kanflo/esparducam/arducam/ov2640_regs.h

#ifndef OV2640_REGS_H
#define OV2640_REGS_H
#include "arducam.h"

const struct sensor_reg OV2640_QVGA[] PROGMEM =
{
	{0xff, 0x0}, 
	{0x2c, 0xff}, 
	{0x2e, 0xdf}, 
	{0xff, 0x1}, 
	{0x3c, 0x32}, 
	{0x11, 0x0}, 
	{0x9, 0x2}, 
	{0x4, 0xa8}, 
	{0x13, 0xe5}, 
	{0x14, 0x48}, 
	{0x2c, 0xc}, 
	{0x33, 0x78}, 
	{0x3a, 0x33}, 
	{0x3b, 0xfb}, 
	{0x3e, 0x0}, 
	{0x43, 0x11}, 
	{0x16, 0x10}, 
	{0x39, 0x2}, 
	{0x35, 0x88}, 

	{0x22, 0xa}, 
	{0x37, 0x40}, 
	{0x23, 0x0}, 
	{0x34, 0xa0}, 
	{0x6, 0x2}, 
	{0x6, 0x88}, 
	{0x7, 0xc0}, 
	{0xd, 0xb7}, 
	{0xe, 0x1}, 
	{0x4c, 0x0}, 
	{0x4a, 0x81}, 
	{0x21, 0x99}, 
	{0x24, 0x40}, 
	{0x25, 0x38}, 
	{0x26, 0x82}, 
	{0x5c, 0x0}, 
	{0x63, 0x0}, 
	{0x46, 0x22}, 
	{0xc, 0x3a}, 
	{0x5d, 0x55}, 
	{0x5e, 0x7d}, 
	{0x5f, 0x7d}, 
	{0x60, 0x55}, 
	{0x61, 0x70}, 
	{0x62, 0x80}, 
	{0x7c, 0x5}, 
	{0x20, 0x80}, 
	{0x28, 0x30}, 
	{0x6c, 0x0}, 
	{0x6d, 0x80}, 
	{0x6e, 0x0}, 
	{0x70, 0x2}, 
	{0x71, 0x94}, 
	{0x73, 0xc1}, 
	{0x3d, 0x34}, 
	{0x12, 0x4}, 
	{0x5a, 0x57}, 
	{0x4f, 0xbb}, 
	{0x50, 0x9c}, 
	{0xff, 0x0}, 
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

	{0x93, 0x6}, 
	{0x93, 0xe3}, 
	{0x93, 0x3}, 
	{0x93, 0x3}, 
	{0x93, 0x0}, 
	{0x93, 0x2}, 
	{0x93, 0x0}, 
	{0x93, 0x0}, 
	{0x93, 0x0}, 
	{0x93, 0x0}, 
	{0x93, 0x0}, 
	{0x93, 0x0}, 
	{0x93, 0x0}, 
	{0x96, 0x0}, 
	{0x97, 0x8}, 
	{0x97, 0x19}, 
	{0x97, 0x2}, 
	{0x97, 0xc}, 
	{0x97, 0x24}, 
	{0x97, 0x30}, 
	{0x97, 0x28}, 
	{0x97, 0x26}, 
	{0x97, 0x2}, 
	{0x97, 0x98}, 
	{0x97, 0x80}, 
	{0x97, 0x0}, 
	{0x97, 0x0}, 
	{0xa4, 0x0}, 
	{0xa8, 0x0}, 
	{0xc5, 0x11}, 
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
	{0x5b, 0x2C},                                   
	{0x5c, 0x05},              //bit2->1;bit[1:0]->1
	{0xd3, 0x02},                                   
	{0xe0, 0x00},                                   
                      
  	{0xff, 0xff},
};  
#endif
